Azemard-Maxime/Athlete-rover-prototype-/Vidéos et images/20220103_174757.jpg

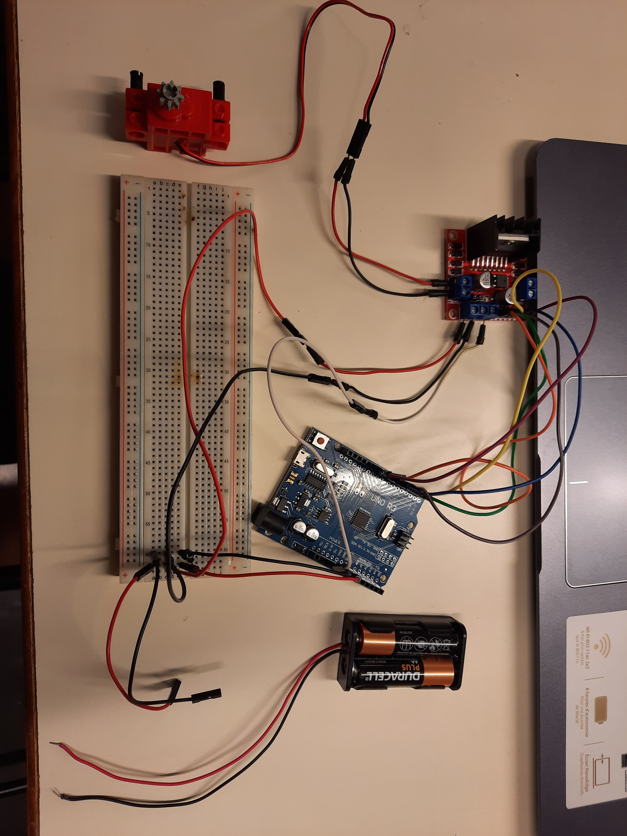
Vidéos et images/20220103_174757.jpg
