Azemard-Maxime/Athlete-rover-prototype-/Vidéos et images/20220218_113729.jpg

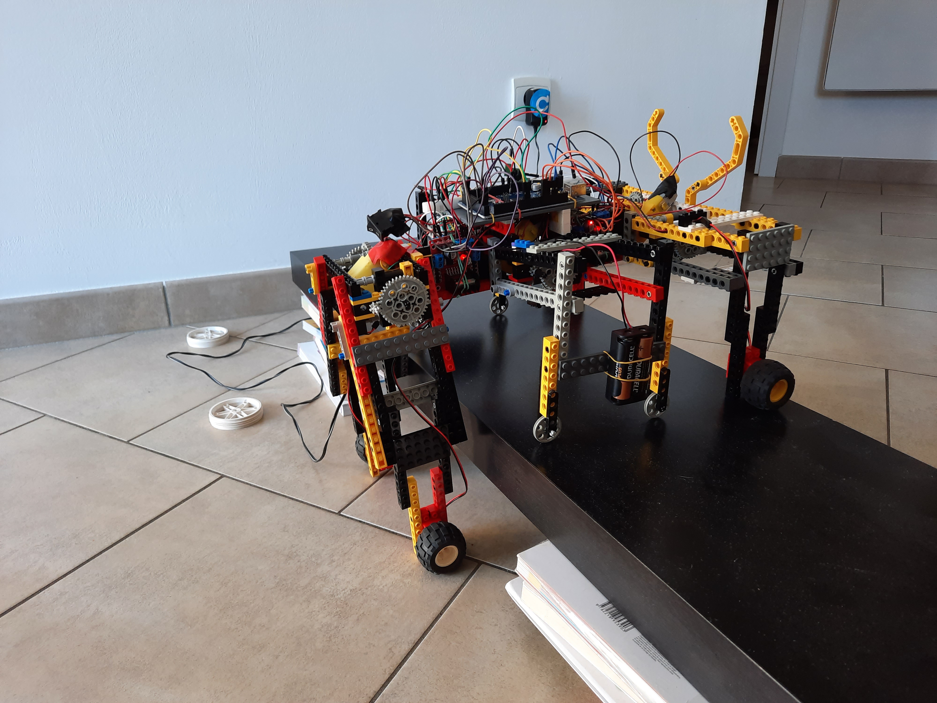
Vidéos et images/20220218_113729.jpg
