Azemard-Maxime/Athlete-rover-prototype-/Vidéos et images/20220218_113739.jpg

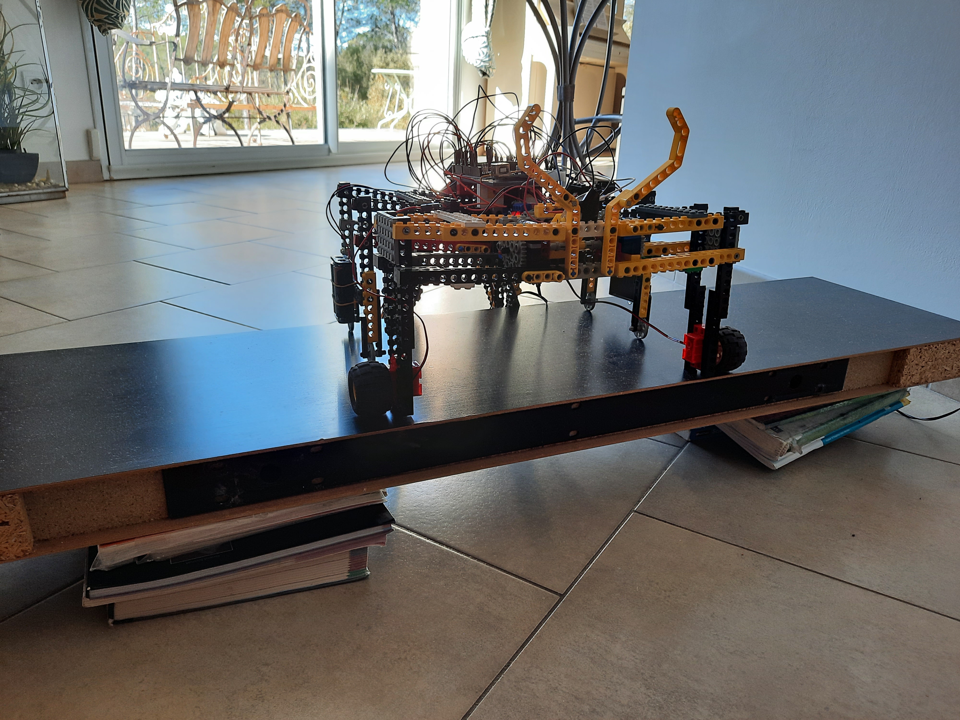
Vidéos et images/20220218_113739.jpg
