Azemard-Maxime/Athlete-rover-prototype-/Vidéos et images/20220228_221752.jpg

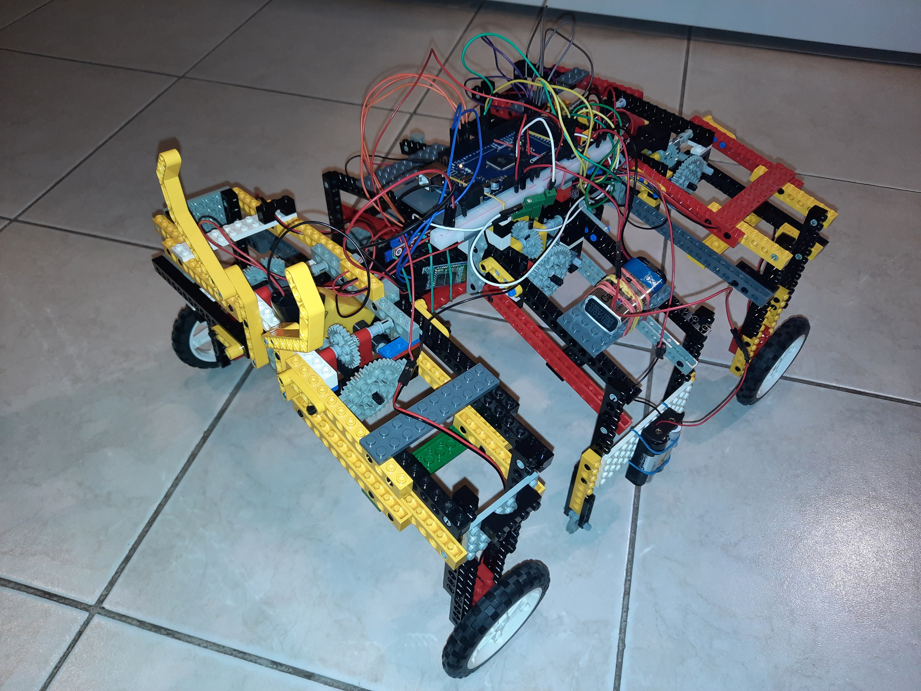
Vidéos et images/20220228_221752.jpg
