Azemard-Maxime/Athlete-rover-prototype-/Codes/MoteurJaune.ino

// Moteur jaune

int moteurJaune = 8;

void setup() {
  // put your setup code here, to run once:
  pinMode(moteurJaune,OUTPUT);
  Serial.begin(9600);
  digitalWrite(moteurJaune,LOW);
}

void loop() {
  // put your main code here, to run repeatedly:

 

}
