Azemard-Maxime/Athlete-rover-prototype-/Vidéos et images/20220109_155608.jpg

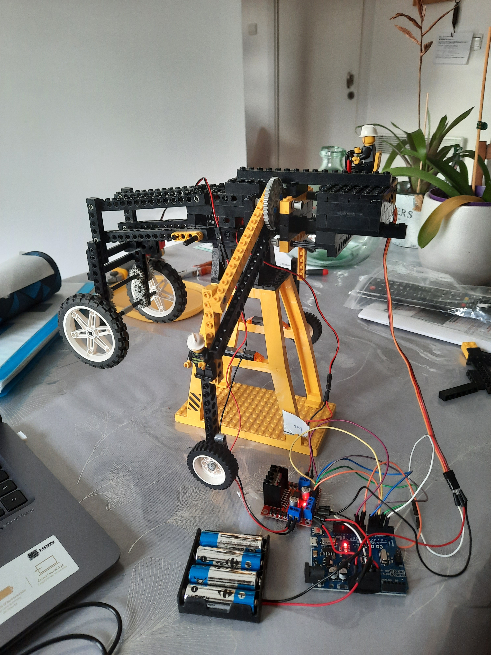
Vidéos et images/20220109_155608.jpg
