Azemard-Maxime/Athlete-rover-prototype-/Vidéos et images/20220228_221831.jpg

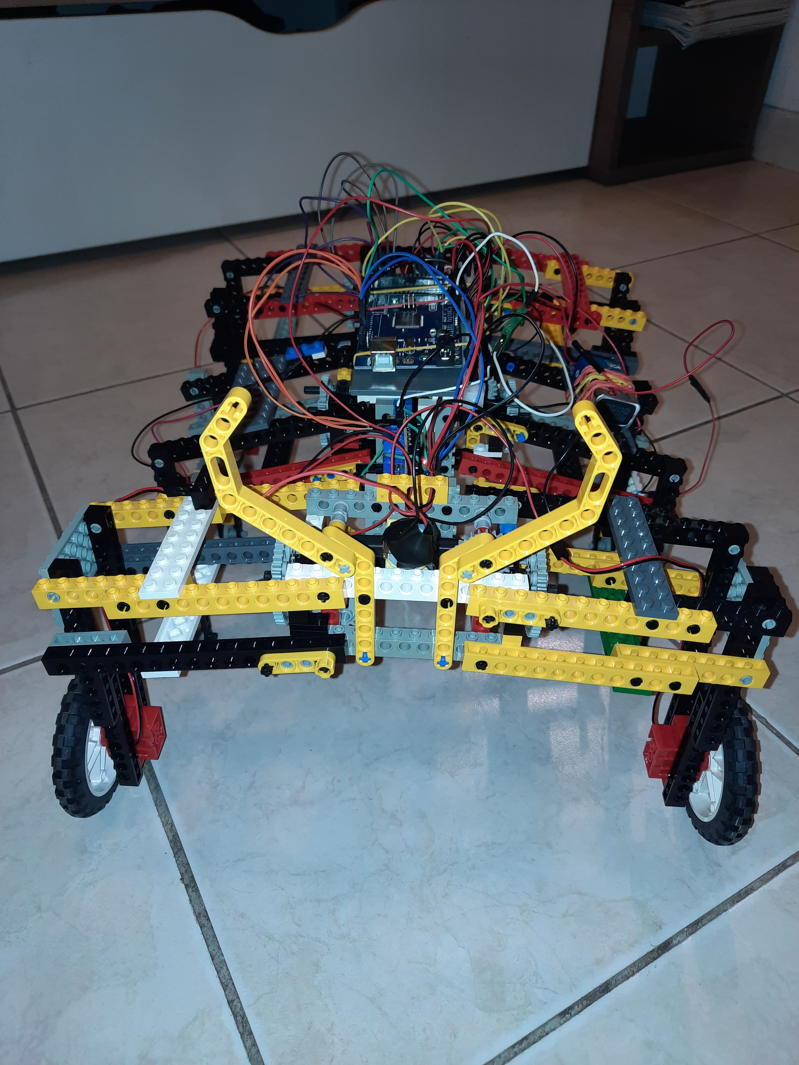
Vidéos et images/20220228_221831.jpg
